thatdecade/OLED-Digital-Dice/Images/IMG_0566.JPG

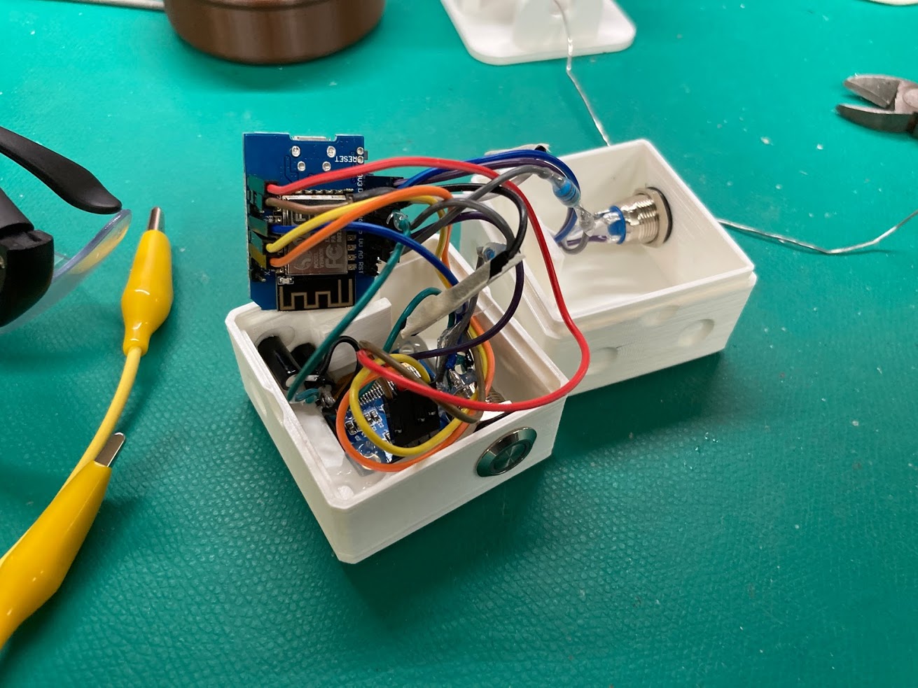
Images/IMG_0566.JPG
