thatdecade/OLED-Digital-Dice/Images/IMG_0567.JPG

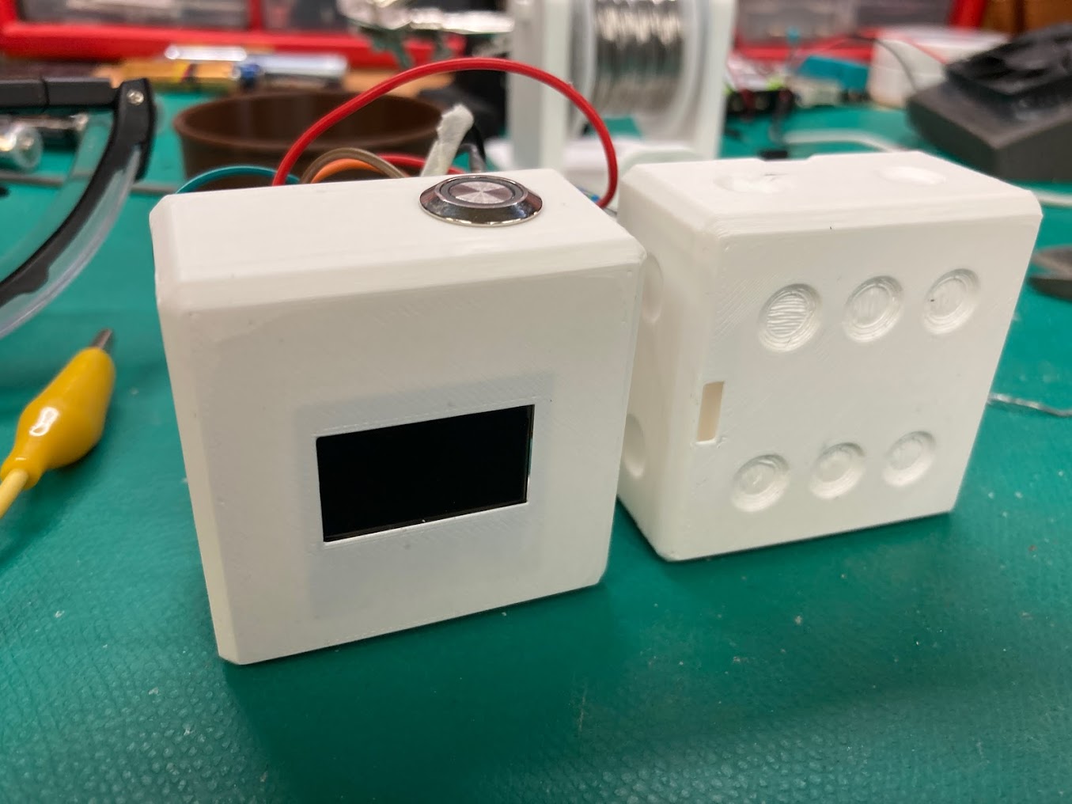
Images/IMG_0567.JPG
